Jasdoge/HalloweenLamps/Assets/main.sch

## EAGLE design Assets/main.sch (2019-10-28)

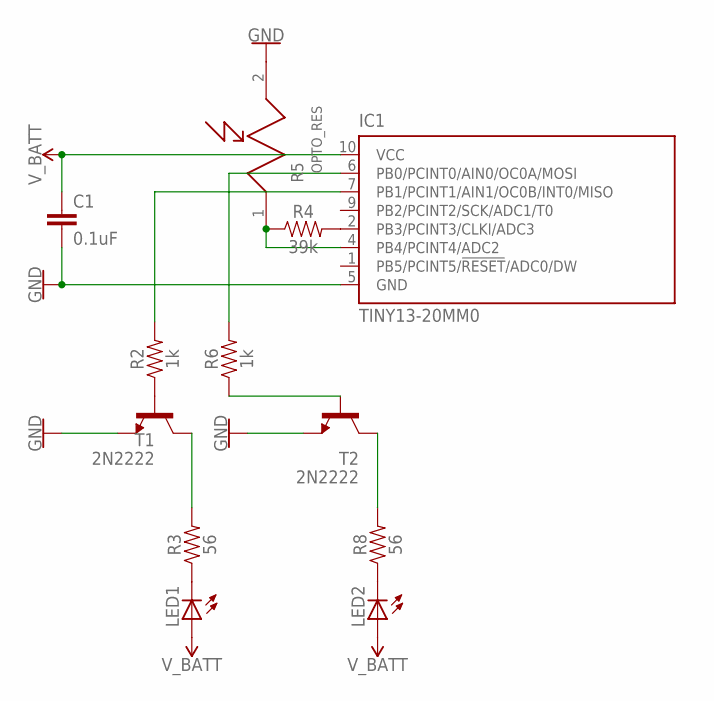
[picture p8: schematic main.sch]

Parts:
C1: 0.1uF; CAP-PTH-SMALL-KIT
IC1: TINY13-20MM0; 10M1
LED1, LED2: LEDTOPLED-SANTANA; MINI-TOPLED-SANTANA
R2, R6: 1k; 0805
R3, R8: 56; 0805
R4: 39k; 0805
R5: OPTO_RES
T1, T2: 2N2222; TO92-EBC-OVAL

Connections:
GND: C1.2, IC1.5 (GND), R5.2, T1.E, T2.E
unnamed: IC1.6 (PB0/PCINT0/AIN0/OC0A/MOSI), R6.2
unnamed: R2.1, T1.B
unnamed: R6.1, T2.B
unnamed: IC1.7 (PB1/PCINT1/AIN1/OC0B/INT0/MISO), R2.2
unnamed: LED1.C, R3.1
unnamed: LED2.C, R8.1
unnamed: R3.2, T1.C
unnamed: R8.2, T2.C
unnamed: IC1.2 (PB3/PCINT3/CLKI/ADC3), R4.2
unnamed: IC1.4 (PB4/PCINT4/ADC2), R4.1, R5.1
V_BATT: C1.1, IC1.10 (VCC), LED1.A, LED2.A
